KenN7/Drone/SolidWorks/Fixation anti-vibra carte.SLDPRT

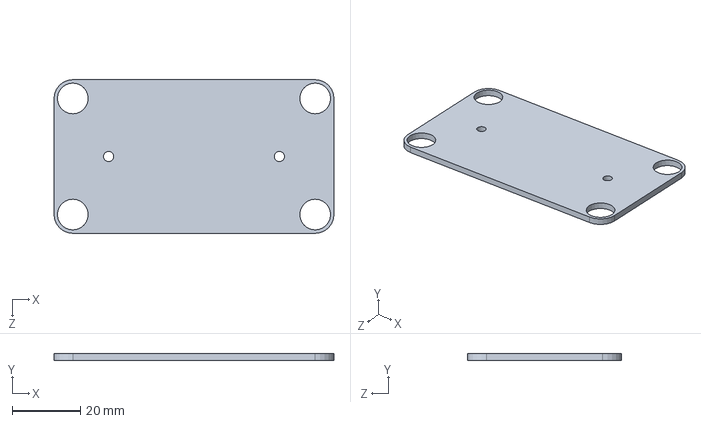
[picture p5: CAD file, 2015-06-30]
SolidWorks/Fixation anti-vibra carte.SLDPRT
82.0 x 2.00 x 45.0 mm
