KenN7/Drone/SolidWorks/junk/Truc flexible pour batterie.SLDPRT

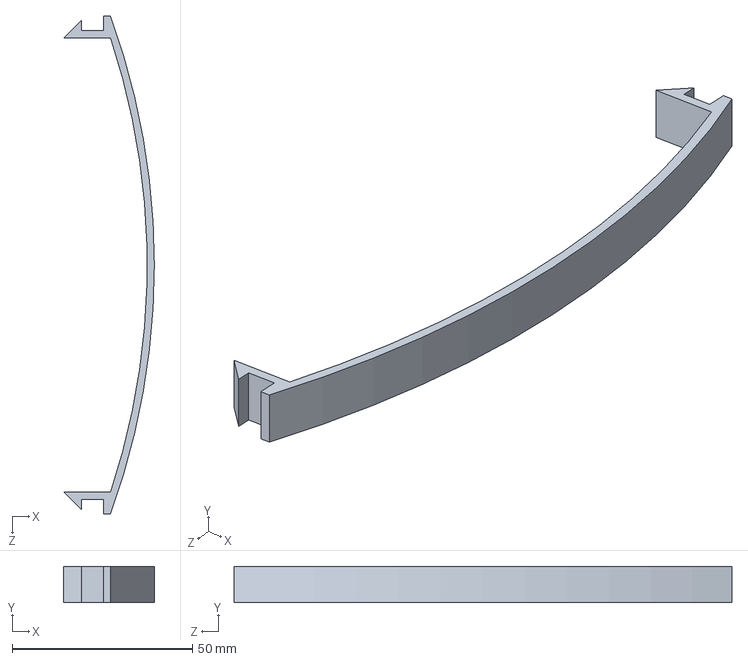
[picture p6: CAD file, 2015-06-23]
SolidWorks/junk/Truc flexible pour batterie.SLDPRT
25.2 x 10.0 x 138.2 mm
