KenN7/Drone/SolidWorks/Base V2 (top).SLDPRT

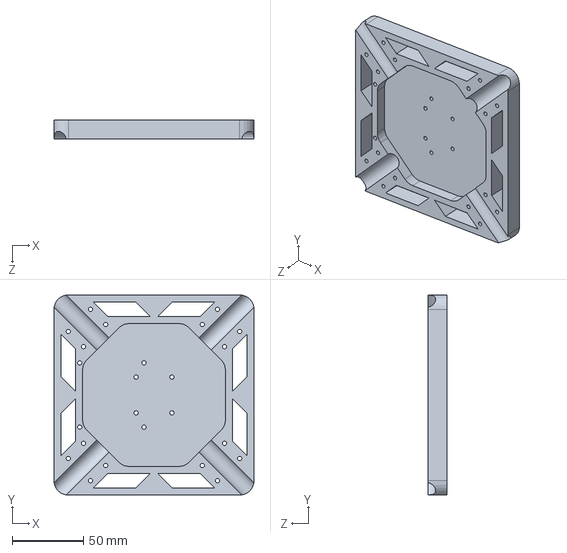
[picture p7: CAD file, 2015-06-23]
SolidWorks/Base V2 (top).SLDPRT
140.0 x 140.0 x 13.5 mm
