KenN7/Drone/SolidWorks/Anti-vibration complet.SLDPRT

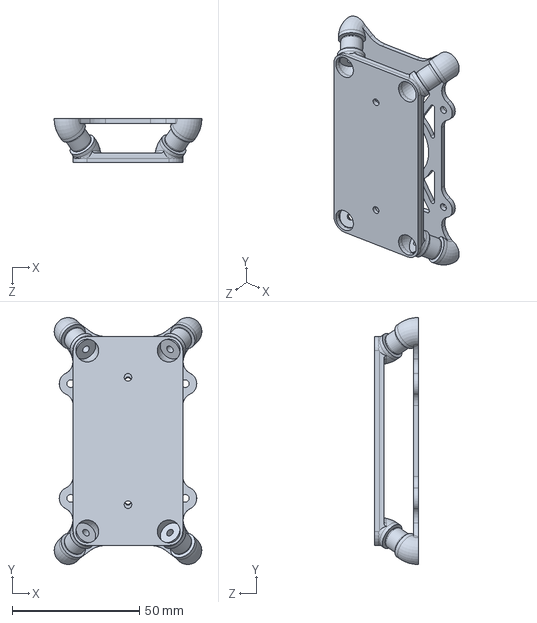
[picture p8: CAD file, 2015-06-23]
SolidWorks/Anti-vibration complet.SLDPRT
58.0 x 97.0 x 17.2 mm
