KenN7/Drone/SolidWorks/Boite batterie (side).SLDPRT

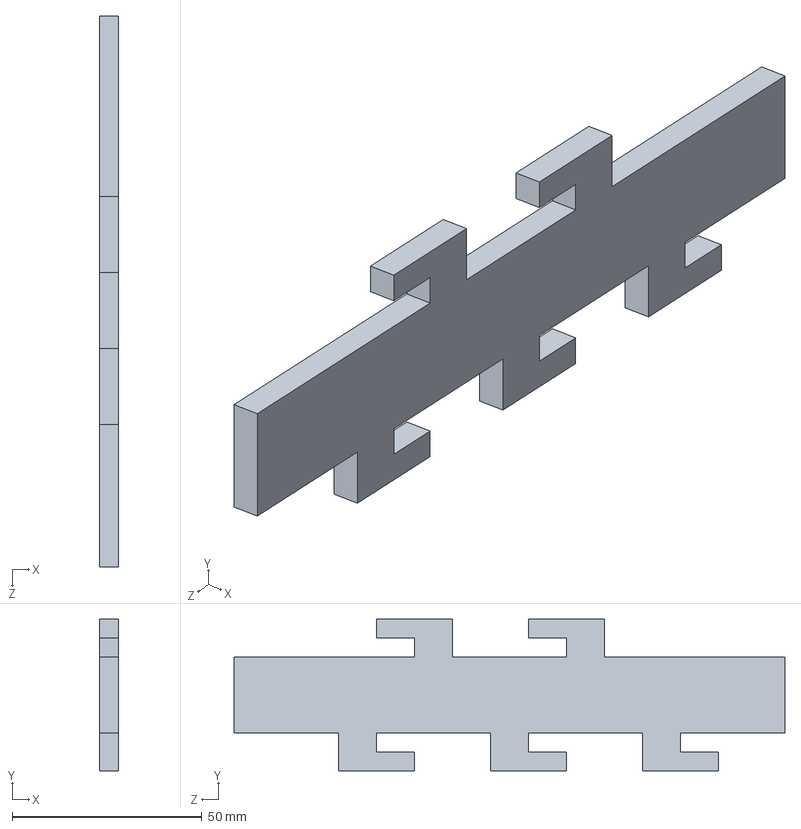
[picture p9: CAD file, 2015-06-23]
SolidWorks/Boite batterie (side).SLDPRT
5.00 x 40.0 x 145.0 mm
