KenN7/Drone/SolidWorks/Support accelero.SLDPRT

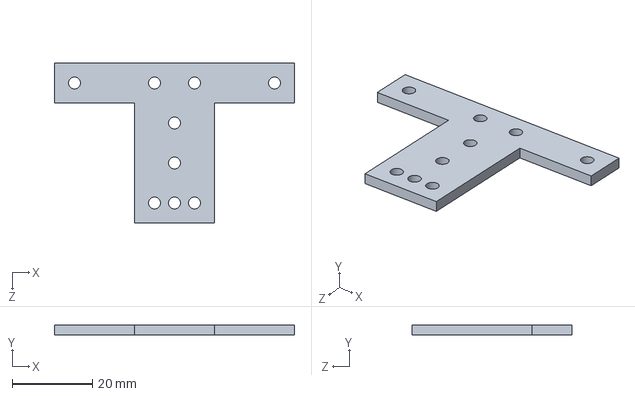
[picture p10: CAD file, 2015-06-23]
SolidWorks/Support accelero.SLDPRT
60.0 x 2.50 x 40.0 mm
