KenN7/Drone/SolidWorks/Boite batterie (bot).SLDPRT

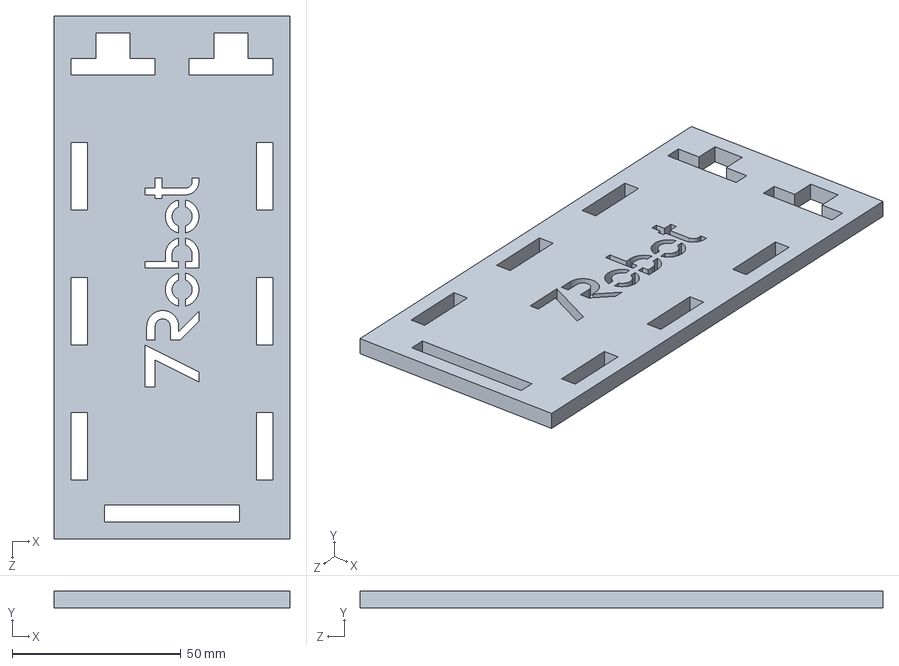
[picture p11: CAD file, 2015-06-23]
SolidWorks/Boite batterie (bot).SLDPRT
70.0 x 5.00 x 155.0 mm
