KenN7/Drone/SolidWorks/Pied.SLDPRT

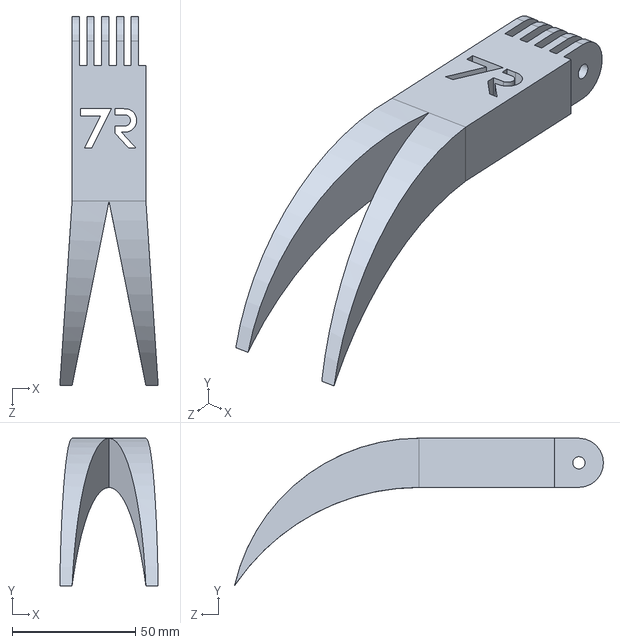
[picture p12: CAD file, 2015-06-23]
SolidWorks/Pied.SLDPRT
40.0 x 60.0 x 150.0 mm
