KenN7/Drone/SolidWorks/Accelero.SLDPRT

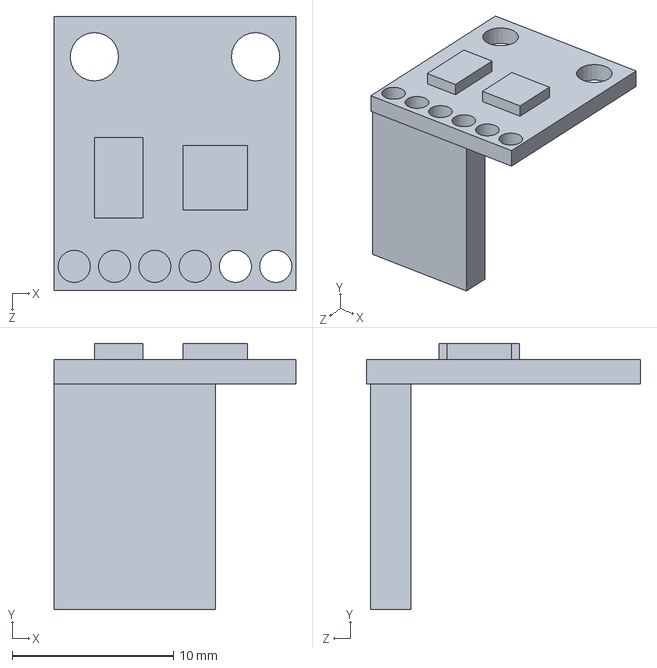
[picture p13: CAD file, 2015-06-23]
SolidWorks/Accelero.SLDPRT
15.0 x 16.5 x 17.0 mm
