KenN7/Drone/SolidWorks/Boite batterie (fond).SLDPRT

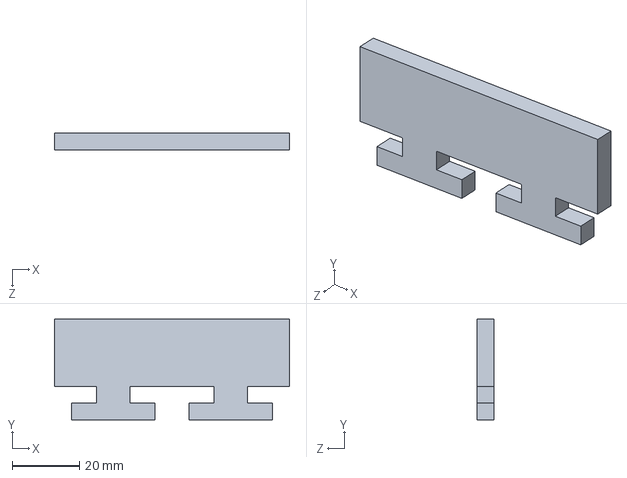
[picture p14: CAD file, 2015-06-23]
SolidWorks/Boite batterie (fond).SLDPRT
70.0 x 30.0 x 5.00 mm
