KenN7/Drone/SolidWorks/Omnimac_APM_Mount_v1.5_bottom_plate.stl

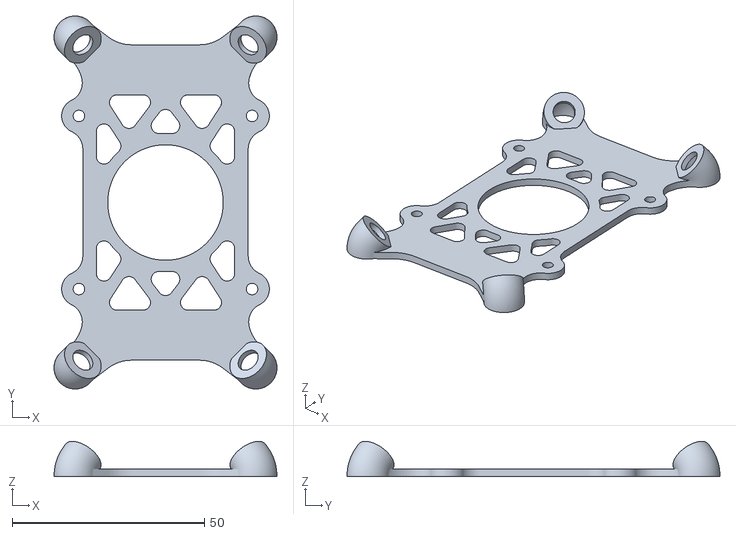
[picture p15: CAD file, 2015-06-18]
SolidWorks/Omnimac_APM_Mount_v1.5_bottom_plate.stl
58.0 x 97.0 x 9.18
