KenN7/Drone/SolidWorks/Omnimac_APM_Mount_v1.5_top_plate.stl

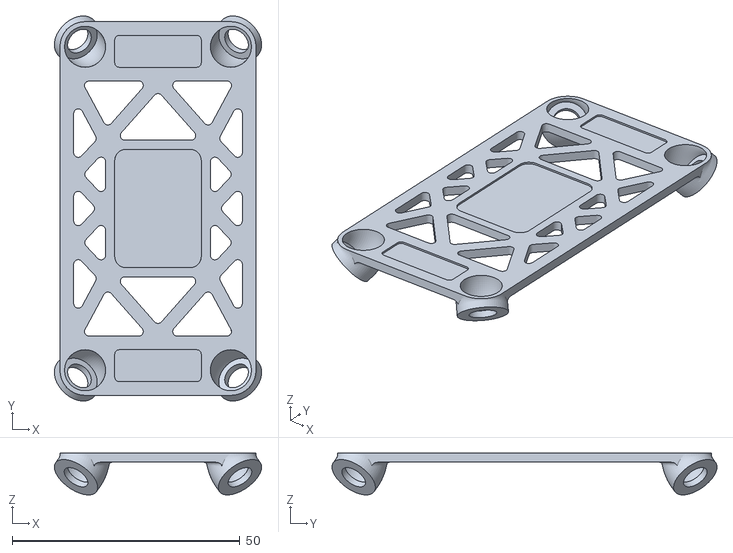
[picture p16: CAD file, 2015-06-18]
SolidWorks/Omnimac_APM_Mount_v1.5_top_plate.stl
45.5 x 84.5 x 9.19
