KenN7/Drone/SolidWorks/Renforcement (bot).SLDPRT

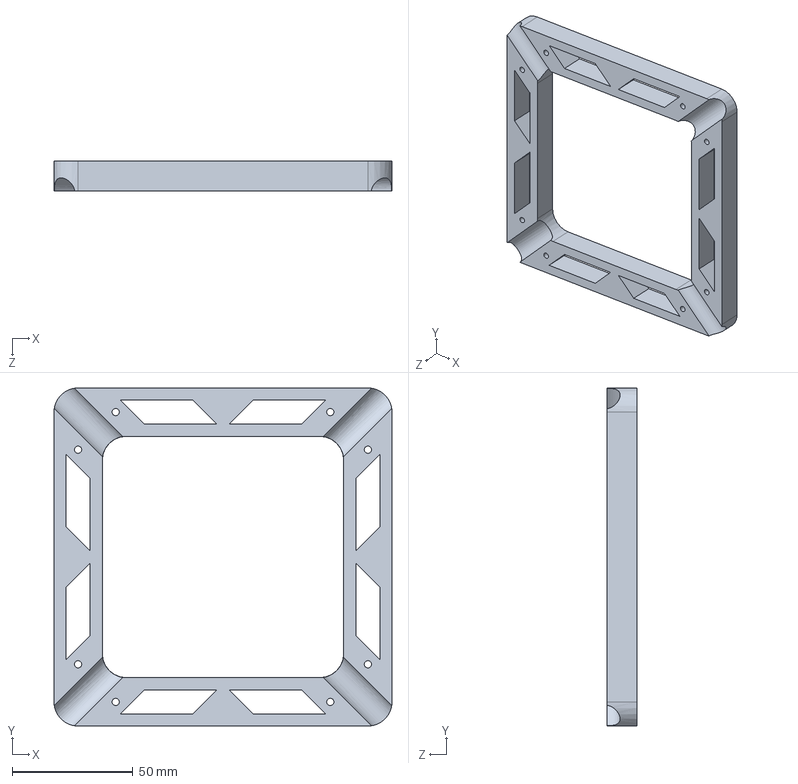
[picture p17: CAD file, 2015-06-18]
SolidWorks/Renforcement (bot).SLDPRT
140.0 x 140.0 x 12.5 mm
