KenN7/Drone/SolidWorks/Renforcement (top).SLDPRT

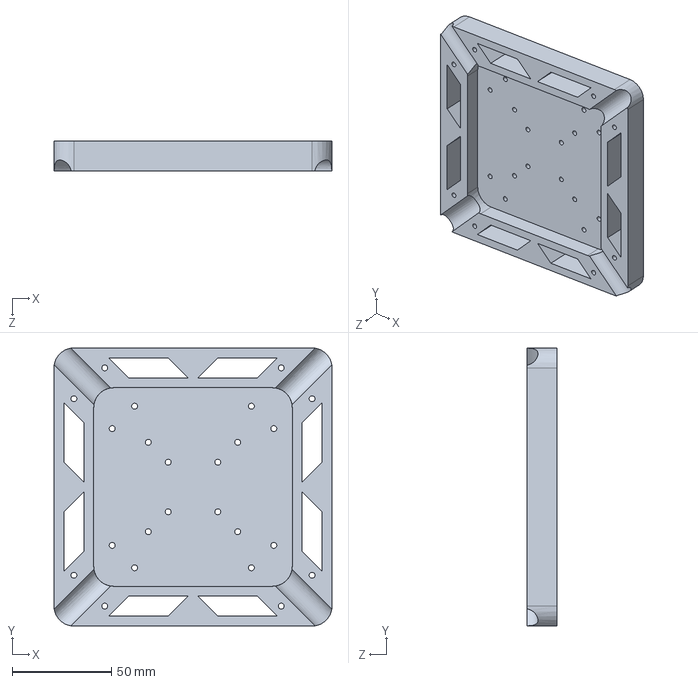
[picture p18: CAD file, 2015-06-18]
SolidWorks/Renforcement (top).SLDPRT
140.0 x 140.0 x 15.0 mm
