KenN7/Drone/SolidWorks/Fixation base.SLDPRT

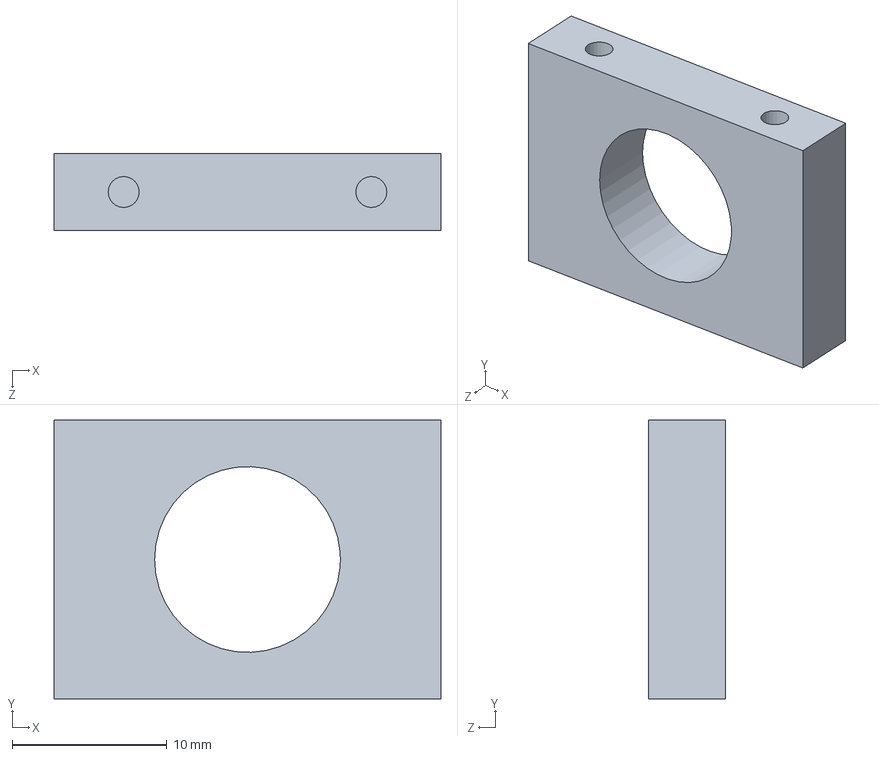
[picture p19: CAD file, 2015-06-17]
SolidWorks/Fixation base.SLDPRT
25.0 x 18.0 x 5.00 mm
