KenN7/Drone/SolidWorks/Fixation pied (bot).SLDPRT

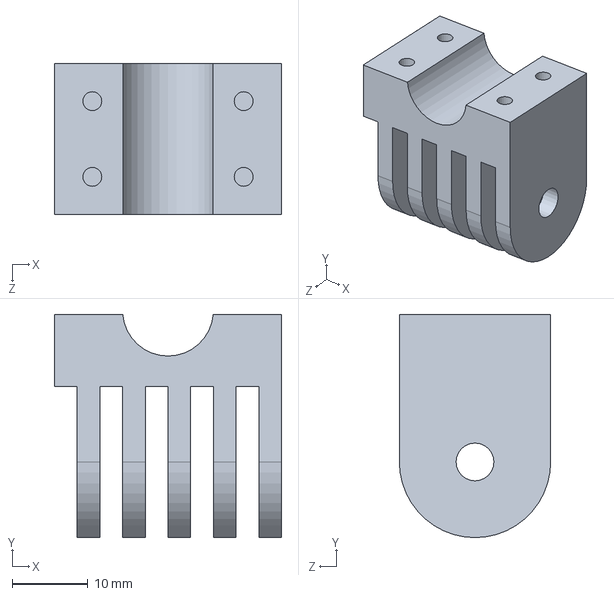
[picture p20: CAD file, 2015-06-17]
SolidWorks/Fixation pied (bot).SLDPRT
30.0 x 29.5 x 20.0 mm
