KenN7/Drone/SolidWorks/Anneau de fixation.SLDPRT

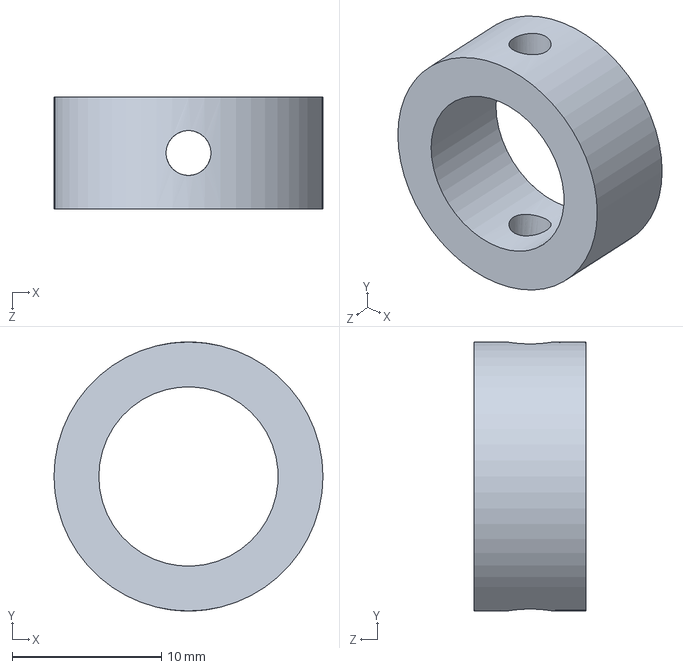
[picture p21: CAD file, 2015-06-17]
SolidWorks/Anneau de fixation.SLDPRT
18.0 x 18.0 x 7.50 mm
