KenN7/Drone/SolidWorks/Support moteur.SLDPRT

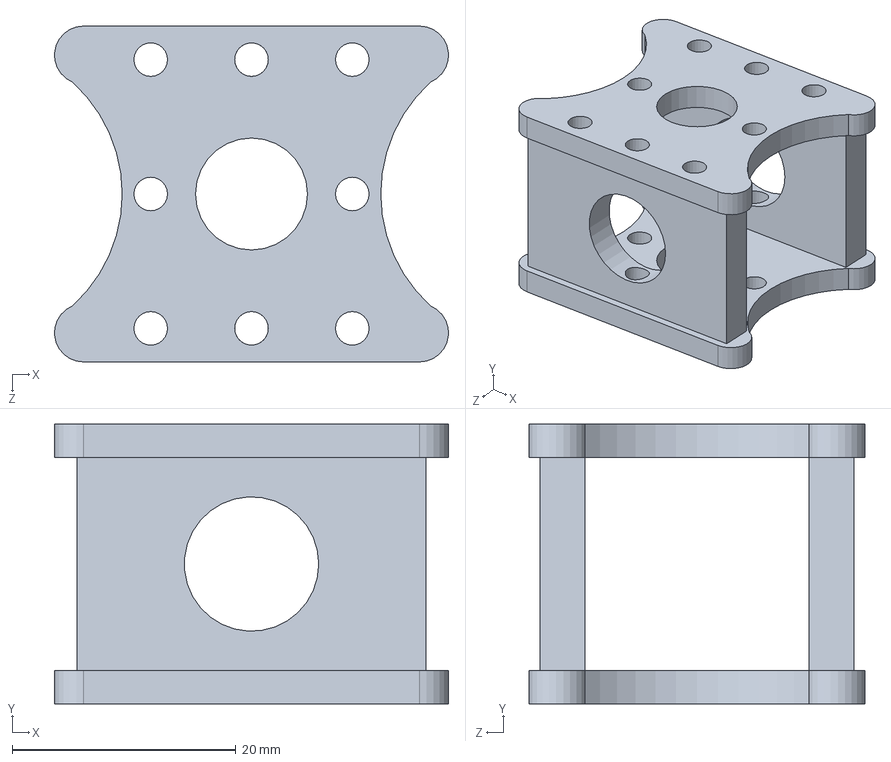
[picture p22: CAD file, 2015-06-17]
SolidWorks/Support moteur.SLDPRT
35.2 x 25.0 x 30.0 mm
