KenN7/Drone/SolidWorks/base (bot).SLDPRT

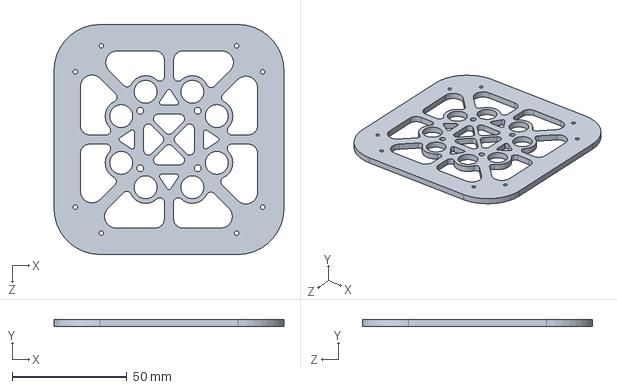
[picture p23: CAD file, 2015-06-17]
SolidWorks/base (bot).SLDPRT
100.0 x 3.00 x 100.0 mm
