KenN7/Drone/SolidWorks/Fixation pied (top).SLDPRT

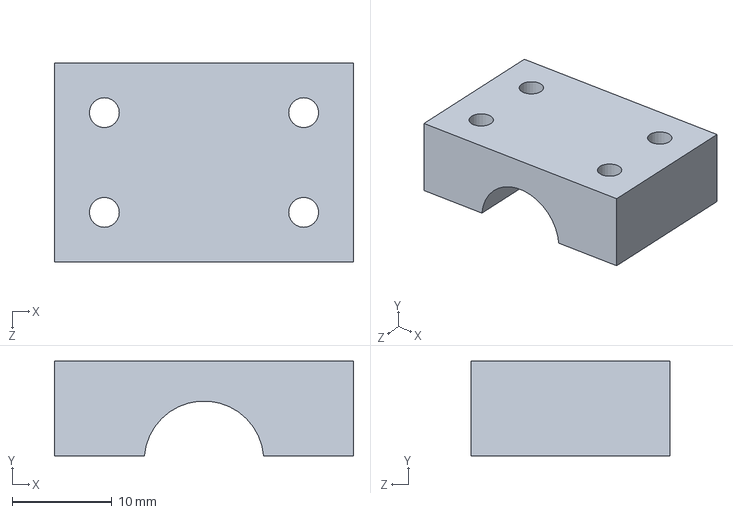
[picture p24: CAD file, 2015-06-17]
SolidWorks/Fixation pied (top).SLDPRT
30.0 x 9.50 x 20.0 mm
