KenN7/Drone/SolidWorks/moteur.SLDPRT

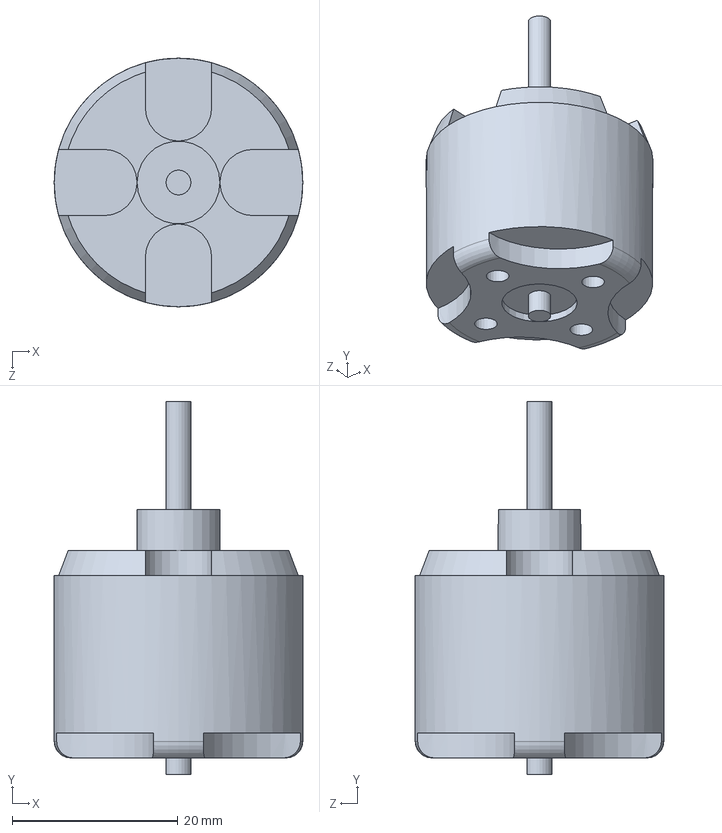
[picture p25: CAD file, 2015-06-17]
SolidWorks/moteur.SLDPRT
30.0 x 45.0 x 30.0 mm
