KenN7/Drone/SolidWorks/Boitier batterie.SLDPRT

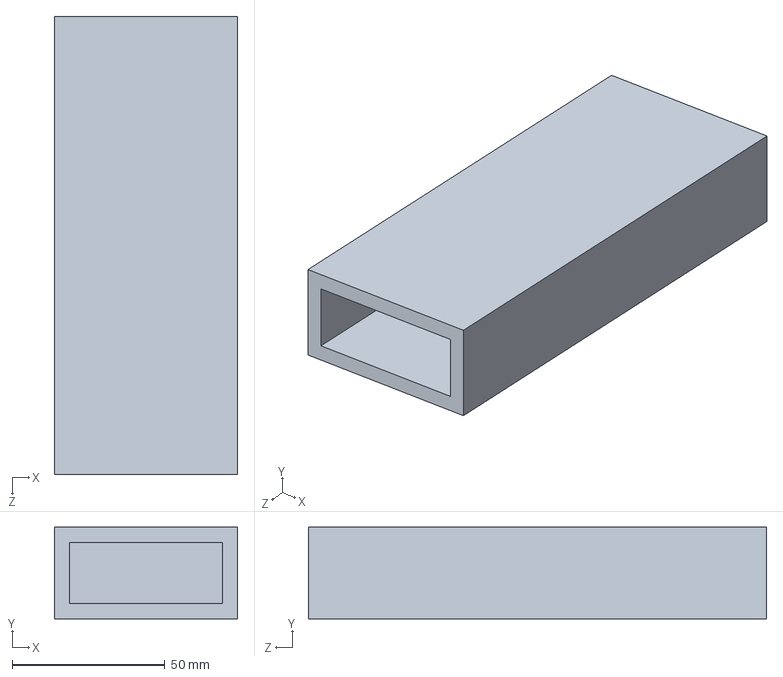
[picture p26: CAD file, 2015-06-17]
SolidWorks/Boitier batterie.SLDPRT
60.0 x 30.0 x 150.0 mm
