KenN7/Drone/SolidWorks/Tube carbone.SLDPRT

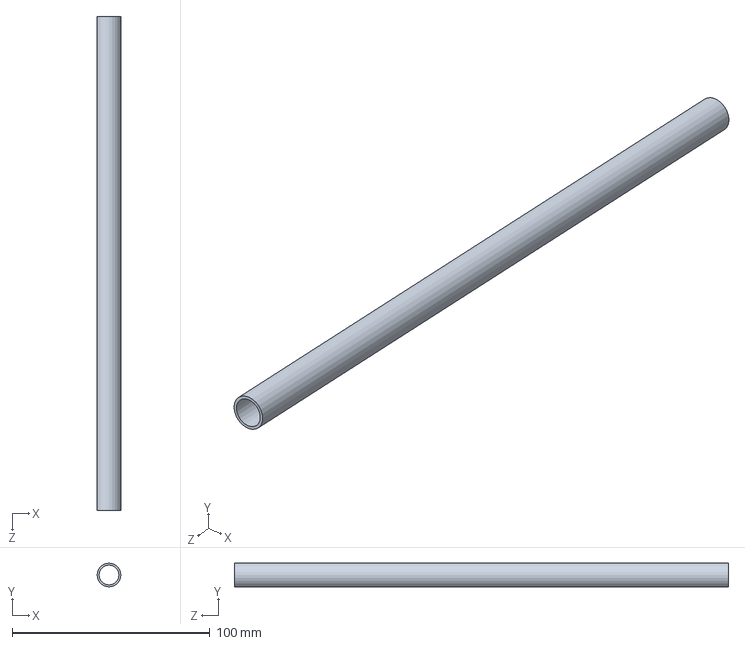
[picture p27: CAD file, 2015-06-17]
SolidWorks/Tube carbone.SLDPRT
12.0 x 12.0 x 250.0 mm
