KenN7/Drone/Drone.X/T1-init-filter.c

/*
* Template dsPIC33F
* Compiler : Microchip xC16
* uC : 33FJ64MC804
* Juillet 2012
*    ____________      _           _
*   |___  /| ___ \    | |         | |
*      / / | |_/ /___ | |__   ___ | |_
*     / /  |    // _ \| '_ \ / _ \| __|
*    / /   | |\ \ (_) | |_) | (_) | |_
*   /_/    |_| \_\___/|____/ \___/'\__|
*			      7robot.fr
*/

/******************************************************************************/
/* Files to Include                                                           */
/******************************************************************************/

#include <p33Fxxxx.h>      /* Includes device header file                     */
#include <stdint.h>        /* Includes uint16_t definition                    */
#include <stdbool.h>       /* Includes true/false definition                  */
#include <stdio.h>
#include "header.h"        /* Function / Parameters                           */
#include <timer.h>
#include "delay.h"
#include <libpic30.h>

/******************************************************************************/
/* User Functions                                                             */
/******************************************************************************/
extern unsigned int InitI2C(void);

void ConfigureOscillator(void)
{
    // Configure PLL prescaler, PLL postscaler, PLL divisor
    PLLFBDbits.PLLDIV = 41; // M=43
    CLKDIVbits.PLLPOST = 0; // N1=2
    CLKDIVbits.PLLPRE  = 0; // N2=2
    // Fosc = M/(N1.N2)*Fin
}

/******************************************************************************/
/* Global variables                                                             */
/******************************************************************************/

volatile int raw_dataA[3];
volatile int raw_dataG[4];
volatile float dataA[2];
volatile float dataG[3];
volatile float filtered_angles[2]={0,0};
volatile float filtered_angles2[2]={0,0};
volatile float filtered_offset[2]={0,0};
volatile float moyenne_X[100]={0};
volatile float moyenne_Y[100]={0};

volatile float filter_xterm[3] = {0,0,0};
volatile float filter_yterm[3] = {0,0,0};

/******************************************************************************/
/* User Functions                                                             */
/******************************************************************************/

void InitApp(void)
{
    //pin des LEDs en sortie
    _TRISA2 = 0;
    _TRISA3 = 0;
    _TRISA4 = 0;
    _TRISA2 = 1;
    _TRISA3 = 1;
    _TRISA4 = 1;
    _TRISC3 = 1;
    _TRISC4 = 1;
    _TRISC5 = 1;
    _TRISB4 = 1;
    _TRISA8 = 1;
    _TRISA9 = 1;
    _TRISC7 = 0;

    _TRISB14 = 0;   //Allim' auxiliaire de l'accelero/gyro mp6050.
    _RB14 = 1;
    
    //Si on a un interrupteur sur la pin RB5 (par exemple), on la met en entree
    //_TRISB5 = 1;
    //Et on active la pullup qui va bien (registres CNPU1 et CNPU2)
    //_CN27PUE = 1;
    // activation de la priorite des interruptions
    _NSTDIS = 0;
    
    AD1PCFGL = 0xFFFF; //desactivation of analog pins

        //LED WARNING :
//    led1 = 1; led2 = 1; led3 = 1; __delay_ms(250); led1 = 0; led2 = 0; led3 = 0; __delay_ms(250);
//    led1 = 1; led2 = 1; led3 = 1; __delay_ms(250); led1 = 0; led2 = 0; led3 = 0; __delay_ms(250);
//    led1 = 1; led2 = 1; led3 = 1; __delay_ms(250); led1 = 0; led2 = 0; led3 = 0; __delay_ms(250);
//    led1 = 1; led2 = 1; led3 = 1;
    Init_UART(); //Init UART for debug
    printf("\nUART oK");
    __delay_ms(250);
    InitI2C();
    __delay_ms(500);

         //Fonction avec l'accel et le gyro 6D0F.
//    test_accel();
//    Initialize_Accel(); //I2C init
//    Initialize_Gyro();
//    Calibrate_Gyro(raw_dataG);

        //Fonction avec l'accel et le gyro MPU6050
    int error = 1;
    do
    {
        Setup_MPU6050();
        MPU6050_Test_I2C();
        error = MPU6050_Check_Registers();
    }
    while(error==1);
    
    __delay_ms(300);
    Calibrate_Gyros();
    // end calib mp6050

    Initialize_T2(); //Timer 2 for Input Capture
    Initialize_IC();

    Initialize_T3(); //Timer 3 for Output compare
    Initialize_OC();

    Initialize_T1(); //Timer 1 for control loop


    Start_OC();
    //OC1RS = 5000;OC2RS = 5000;OC3RS = 5000;OC4RS = 5000;

    __delay_ms(1000);

    ReStart_T1();
}

// Some functions definitions
void Initialize_T1()
{
    OpenTimer1(T1_OFF & T1_GATE_OFF & T1_PS_1_8 & T1_SOURCE_INT, 12500);
    ConfigIntTimer1(T1_INT_PRIOR_3 & T1_INT_ON);
}

void ReStart_T1()
{
    T1CONbits.TON = 0;
    WriteTimer1(0);
    T1CONbits.TON = 1;
}

//Runs a complementary filter configured via coef c_filter (in header.h)

/*!\ TODO CHECKER SI LES NUMEROS DE TABLEAUX CORRESPONDENT AUX MEMES ANGLES !!! /!\*/

void Complementary_filter(volatile float * filtered, volatile float * data_gyro, volatile float * data_accel)
{
    filtered[0] = data_gyro[0]*(c_filter) + data_accel[0]*(1-c_filter); // Here gyro is an angle
    filtered[1] = data_gyro[1]*(c_filter) + data_accel[1]*(1-c_filter);
    //filtered_value = (value + gyro*dt)*c_filter + accel*(1-c_filter); // Here gyro is a rate (angle/dt)
    //COMPLEMENTARY_YANGLE = (COMPLEMENTARY_YANGLE + GYRO_YRATE*dt)*a + ACCEL_YANGLE*(1-a);
    //il faut faire confiance au gyro et corriger avec l'accel !!!
}

int Ck = 1;

void Snd_filter(volatile float * filtered, volatile float * data_gyro, volatile float * data_accel)
{
    filter_xterm[0] = (data_accel[0] - filtered[0]) * timeConstant * timeConstant;
    filter_yterm[0] = (data_accel[1] - filtered[1]) * timeConstant * timeConstant;
    filter_xterm[2] += (dt * filter_xterm[0]);
    filter_yterm[2] += (dt * filter_yterm[0]);
    filter_xterm[1] = filter_xterm[2] + (data_accel[0] - filtered[0]) * 2 * timeConstant + data_gyro[0] * Ck;
    filter_yterm[1] = filter_yterm[2] + (data_accel[1] - filtered[1]) * 2 * timeConstant + data_gyro[1] * Ck;

    filtered[0] += (dt * filter_xterm[1]);
    filtered[1] += (dt * filter_yterm[1]);
}

void second_order_complementary_filter() //http://code.google.com/p/aeroquad/source/browse/trunk/AeroQuad/Filter.pde?r=143
{
    filter_xterm[0] = (ACCEL_XANGLE - COMPLEMENTARY_XANGLE) * timeConstant * timeConstant;
    filter_yterm[0] = (ACCEL_YANGLE - COMPLEMENTARY_YANGLE) * timeConstant * timeConstant;
    filter_xterm[2] = (dt * filter_xterm[0]) + filter_xterm[2];
    filter_yterm[2] = (dt * filter_yterm[0]) + filter_yterm[2];
    filter_xterm[1] = filter_xterm[2] + (ACCEL_XANGLE - COMPLEMENTARY_XANGLE) * 2 * timeConstant + GYRO_XRATE;
    filter_yterm[1] = filter_yterm[2] + (ACCEL_YANGLE - COMPLEMENTARY_YANGLE) * 2 * timeConstant + GYRO_YRATE;
    COMPLEMENTARY_XANGLE = (dt * filter_xterm[1]) + COMPLEMENTARY_XANGLE;
    COMPLEMENTARY_YANGLE = (dt * filter_yterm[1]) + COMPLEMENTARY_YANGLE;
}

void filtre_moyennant(volatile float * filtered, volatile float * data)
{
    int i=0;
    for (i=0; i<99; i++)
    {
        moyenne_X[i+1]=moyenne_X[i];
        moyenne_Y[i+1]=moyenne_Y[i];
    }
    moyenne_X[0]=data[0];
    moyenne_Y[0]=data[1];
    
    float moyenne_X_sum=0;
    float moyenne_Y_sum=0;
    i=0;
    for (i=0; i<100; i++)
    {
        moyenne_X_sum += moyenne_X[i];
        moyenne_Y_sum += moyenne_Y[i];
    }
    filtered[0]=moyenne_X_sum/100;
    filtered[1]=moyenne_Y_sum/100;
}

/******************************************************************************/
/* Interrupt Routines                                                         */
/******************************************************************************/
/* Add interrupt routine code here. */
extern float filteredOutput[3];

void __attribute__((interrupt, auto_psv)) _T1Interrupt(void)
{
    _T1IF = 0;      // On baisse le FLAG
//    Read_Accel(raw_dataA);
    //smoothSensorReadings();
//    Read_Gyro(raw_dataG);
//    Process_Accel(raw_dataA, dataA);
//    Process_Gyro(raw_dataG, dataG);
    Get_Gyro_Rates(dataG);
    Get_Accel_Values();
    Get_Accel_Angles(dataA);
    smoothSensorReadings();
    Complementary_filter(filtered_angles, dataG, filteredOutput);
    //filtre_moyennant(filtered_angles2, filtered_angles);
    Snd_filter(filtered_angles, dataG, dataA);
    //second_order_complementary_filter();
    
    //printf("%g,%g,%g,%g\n",(double)filtered_angles[0],(double)dataG[0],(double)dataA[0],(double)filtered_angles2[0]);
    static int y=0;
    if (y%100 == 1) {
        printf("%g,%g\n",(double)filtered_angles[0],(double)filtered_angles[1]);
        //printf("%g\n", (double)dataG[2]);
    }
    y+=1;
    //printf("%f,%f,%f\n",COMPLEMENTARY_XANGLE,GYRO_XRATE,ACCEL_XANGLE);
    //min motor 6500; ??
    PID();
    Update_PWM();
    //testmoteurs();
    
//    led1 = !led1;    // On bascule l'etat de la LED
}

void noInterrupts(void){
    _IPL0=1;
    _IPL1=1;
    _IPL2=1;
}

void reInterrupts(void){
    _IPL0=0;
    _IPL1=0;
    _IPL2=0;
}


/******************************************************************************/
/* Interrupt Vector Options                                                   */
/******************************************************************************/
/*                                                                            */
/* Refer to the C30 (MPLAB C Compiler for PIC24F MCUs and dsPIC33F DSCs) User */
/* Guide for an up to date list of the available interrupt options.           */
/* Alternately these names can be pulled from the device linker scripts.      */
/*                                                                            */
/* dsPIC33F Primary Interrupt Vector Names:                                   */
/*                                                                            */
/* _INT0Interrupt      _C1Interrupt                                           */
/* _IC1Interrupt       _DMA3Interrupt                                         */
/* _OC1Interrupt       _IC3Interrupt                                          */
/* _T1Interrupt        _IC4Interrupt                                          */
/* _DMA0Interrupt      _IC5Interrupt                                          */
/* _IC2Interrupt       _IC6Interrupt                                          */
/* _OC2Interrupt       _OC5Interrupt                                          */
/* _T2Interrupt        _OC6Interrupt                                          */
/* _T3Interrupt        _OC7Interrupt                                          */
/* _SPI1ErrInterrupt   _OC8Interrupt                                          */
/* _SPI1Interrupt      _DMA4Interrupt                                         */
/* _U1RXInterrupt      _T6Interrupt                                           */
/* _U1TXInterrupt      _T7Interrupt                                           */
/* _ADC1Interrupt      _SI2C2Interrupt                                        */
/* _DMA1Interrupt      _MI2C2Interrupt                                        */
/* _SI2C1Interrupt     _T8Interrupt                                           */
/* _MI2C1Interrupt     _T9Interrupt                                           */
/* _CNInterrupt        _INT3Interrupt                                         */
/* _INT1Interrupt      _INT4Interrupt                                         */
/* _ADC2Interrupt      _C2RxRdyInterrupt                                      */
/* _DMA2Interrupt      _C2Interrupt                                           */
/* _OC3Interrupt       _DCIErrInterrupt                                       */
/* _OC4Interrupt       _DCIInterrupt                                          */
/* _T4Interrupt        _DMA5Interrupt                                         */
/* _T5Interrupt        _U1ErrInterrupt                                        */
/* _INT2Interrupt      _U2ErrInterrupt                                        */
/* _U2RXInterrupt      _DMA6Interrupt                                         */
/* _U2TXInterrupt      _DMA7Interrupt                                         */
/* _SPI2ErrInterrupt   _C1TxReqInterrupt                                      */
/* _SPI2Interrupt      _C2TxReqInterrupt                                      */
/* _C1RxRdyInterrupt                                                          */
/*                                                                            */
/* For alternate interrupt vector naming, simply add 'Alt' between the prim.  */
/* interrupt vector name '_' and the first character of the primary interrupt */
/* vector name.  There is no Alternate Vector or 'AIVT' for the 33E family.   */
/*                                                                            */
/* For example, the vector name _ADC2Interrupt becomes _AltADC2Interrupt in   */
/* the alternate vector table.                                                */
/*                                                                            */
/* Example Syntax:                                                            */
/*                                                                            */
/* void __attribute__((interrupt,auto_psv)) <Vector Name>(void)               */
/* {                                                                          */
/*     <Clear Interrupt Flag>                                                 */
/* }                                                                          */
/*                                                                            */
/* For more comprehensive interrupt examples refer to the C30 (MPLAB C        */
/* Compiler for PIC24 MCUs and dsPIC DSCs) User Guide in the                  */
/* <compiler installation directory>/doc directory for the latest compiler    */
/* release.                                                                   */
/*                                                                            */
