KenN7/Drone/Drone.X/outputcompare.c

/* 
 * File:   outputcompare.c
 * Author: Ken
 *
 * Created on 27 avril 2013, 14:51
 */

#include <p33Fxxxx.h>      /* Includes device header file                     */
#include <stdint.h>        /* Includes uint16_t definition                    */
#include <stdbool.h>       /* Includes true/false definition                  */
#include "header.h"        /* Function / Parameters                           */
#include <libpic30.h>
#include <stdio.h>
#include <stdlib.h>
#include <outcompare.h>
#include <timer.h>

/*
 * 
 */

void Initialize_T3()
{
    OpenTimer3(T3_OFF & T3_GATE_OFF & T3_PS_1_8 & T3_SOURCE_INT, 12500);
    DisableIntT3;
}

void ReStart_T3()
{
    T3CONbits.TON = 0;
    WriteTimer3(0);
    T3CONbits.TON = 1;
}
void Initialize_OC()
{
    UnlockRP;
    _RP10R = 0b10010; //Tie OC1 to RP10 (PWM1)
    _RP11R = 0b10011; //Tie OC2 to RP11 (PWM2)
    _RP12R = 0b10100; //Tie OC3 to RP12 (PWM3)
    _RP13R = 0b10101; //Tie OC4 to RP13 (PWM4)
    LockRP;

    OpenOC1(OC_IDLE_CON & OC_TIMER3_SRC & OC_OFF, 1000, 0);
    OpenOC2(OC_IDLE_CON & OC_TIMER3_SRC & OC_OFF, 1000, 0);
    OpenOC3(OC_IDLE_CON & OC_TIMER3_SRC & OC_OFF, 1000, 0);
    OpenOC4(OC_IDLE_CON & OC_TIMER3_SRC & OC_OFF, 1000, 0); //dans l'ordre OCxRS et OCxR

    ConfigIntOC1(OC_INT_OFF & OC_INT_PRIOR_2);
    ConfigIntOC2(OC_INT_OFF & OC_INT_PRIOR_2);
    ConfigIntOC3(OC_INT_OFF & OC_INT_PRIOR_2);
    ConfigIntOC4(OC_INT_OFF & OC_INT_PRIOR_2);
}
// Pour changer la largeur du PWM il faut mettre OCxRS entre 5000 (1ms) et 10000 (2ms)
void Start_OC()
{
    OC1CONbits.OCM = 0b110; //OC_PWM_FAULT_PIN_ENABLE
    OC2CONbits.OCM = 0b110;
    OC3CONbits.OCM = 0b110;
    OC4CONbits.OCM = 0b110;
    ReStart_T3();
}
